aditya27b/HackNest-SIH/skematics/SIH hacknest.kicad_sch

## KiCad design skematics/SIH hacknest.kicad_sch (2026-06-04)

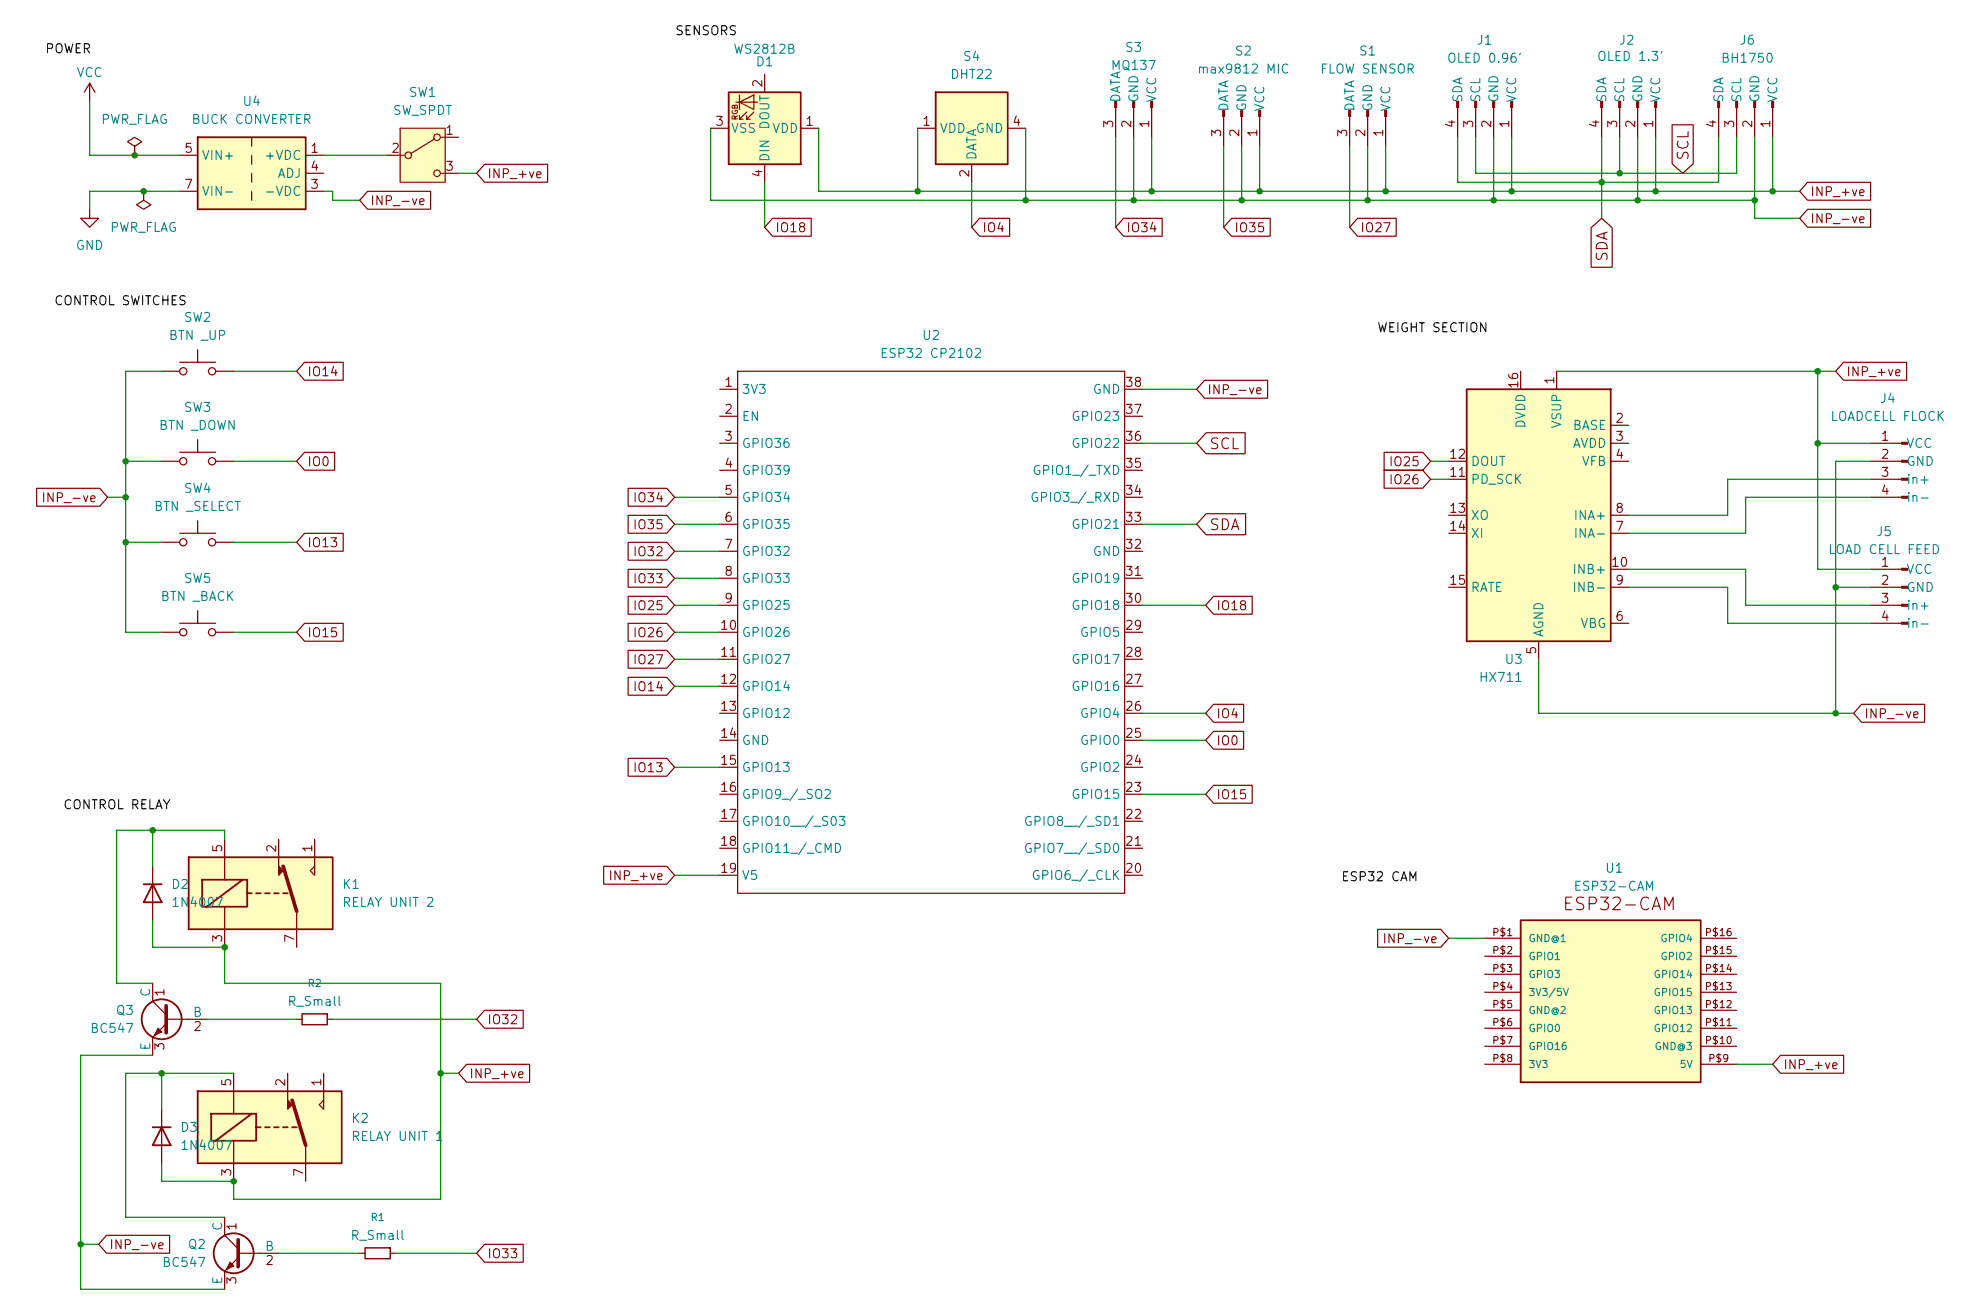
[picture p4: schematic SIH hacknest.kicad_sch]

Parts:
D1: WS2812B; LED_WS2812B_PLCC4_5.0x5.0mm_P3.2mm
D2, D3: 1N4007; D_DO-41_SOD81_P10.16mm_Horizontal
J1: OLED 0.96'
J2: OLED 1.3'
J4: LOADCELL FLOCK
J5: LOAD CELL FEED
J6: BH1750
K1: RELAY UNIT 2; Relay_SPDT_StandexMeder_SIL_Form1C
K2: RELAY UNIT 1; Relay_SPDT_StandexMeder_SIL_Form1C
Q2, Q3: BC547; TO-92_Inline
R1, R2: R_Small
S1: FLOW SENSOR
S2: max9812 MIC
S3: MQ137
S4: DHT22; Aosong_DHT11_5.5x12.0_P2.54mm
SW1: SW_SPDT
SW2: BTN _UP
SW3: BTN _DOWN
SW4: BTN _SELECT
SW5: BTN _BACK
U1: ESP32-CAM
U2: ESP32 CP2102; ESP32_38Pin
U3: HX711; SOIC-16_3.9x9.9mm_P1.27mm
U4: BUCK CONVERTER; Converter_DCDC_Silvertel_Ag99xxLP_THT

Connections:
GND: U4.7 (VIN-), U4.8 (VIN-)
INP_+ve: D1.1 (VDD), D2.2 (A), D3.2 (A), J1.1 (VCC), J2.1 (VCC), J4.1 (VCC), J5.1 (VCC), J6.1 (VCC), K1.3, K2.3, S1.1 (VCC), S2.1 (VCC), S3.1 (VCC), S4.1 (VDD), SW1.3 (C), U1.P$9 (5V), U2.19 (V5), U3.1 (VSUP)
INP_-ve: D1.3 (VSS), J1.2 (GND), J2.2 (GND), J4.2 (GND), J5.2 (GND), J6.2 (GND), Q2.3 (E), Q3.3 (E), S1.2 (GND), S2.2 (GND), S3.2 (GND), S4.4 (GND), SW2.1, SW3.1, SW4.1, SW5.1, U1.P$1 (GND@1), U2.38 (GND), U3.5 (AGND), U4.3 (-VDC)
IO0: SW3.2, U2.25 (GPIO0)
IO4: S4.2 (DATA), U2.26 (GPIO4)
IO13: SW4.2, U2.15 (GPIO13)
IO14: SW2.2, U2.12 (GPIO14)
IO15: SW5.2, U2.23 (GPIO15)
IO18: D1.4 (DIN), U2.30 (GPIO18)
IO25: U2.9 (GPIO25), U3.12 (DOUT)
IO26: U2.10 (GPIO26), U3.11 (PD_SCK)
IO27: S1.3 (DATA), U2.11 (GPIO27)
IO32: R2.1, U2.7 (GPIO32)
IO33: R1.1, U2.8 (GPIO33)
IO34: S3.3 (DATA), U2.5 (GPIO34)
IO35: S2.3 (DATA), U2.6 (GPIO35)
unnamed: D2.1 (K), K1.5, Q3.1 (C)
unnamed: D3.1 (K), K2.5, Q2.1 (C)
unnamed: J4.3 (in+), U3.8 (INA+)
unnamed: J4.4 (in-), U3.7 (INA-)
unnamed: J5.3 (in+), U3.10 (INB+)
unnamed: J5.4 (in-), U3.9 (INB-)
unnamed: Q2.2 (B), R1.2
unnamed: Q3.2 (B), R2.2
unnamed: SW1.2 (B), U4.1 (+VDC), U4.2 (+VDC)
SCL: J1.3 (SCL), J2.3 (SCL), J6.3 (SCL), U2.36 (GPIO22)
SDA: J1.4 (SDA), J2.4 (SDA), J6.4 (SDA), U2.33 (GPIO21)
VCC: U4.5 (VIN+), U4.6 (VIN+)
